UoA-Maker-Club/smart-lanterns/smart-lanterns/conf.h

#define BAUD_RATE         115200

// LED SETTINGS
#define LED_PIN   D4
#define LED_COUNT 18


// WIFI SETTINGS
#define WIFI_SSID         "UoA-Unleash"
#define WIFI_PASS         "UoA_Unl3ash"

// Sinric Pro
#define LIGHT_ID          "xxxxxxxxxxxxxxxxxxxxxxxx"
#define APP_KEY           "d6d37047-xxxx-xxxx-xxxx-xxxxxxxxxxxx"
#define APP_SECRET        "xxxxxxxx-xxxx-xxxx-xxxx-xxxxxxxxxxxx-xxxxxxx-xxxx-xxxx-xxxx-xxxxxxxxxxxx"


#define HUE 200
#define PATTERN 1

/*
  0 -> Trail
  1 -> rainbow trail
  2 -> still
*/
